CogPlatform/CageLab/manufacture/plate/europe/core_top.dxf

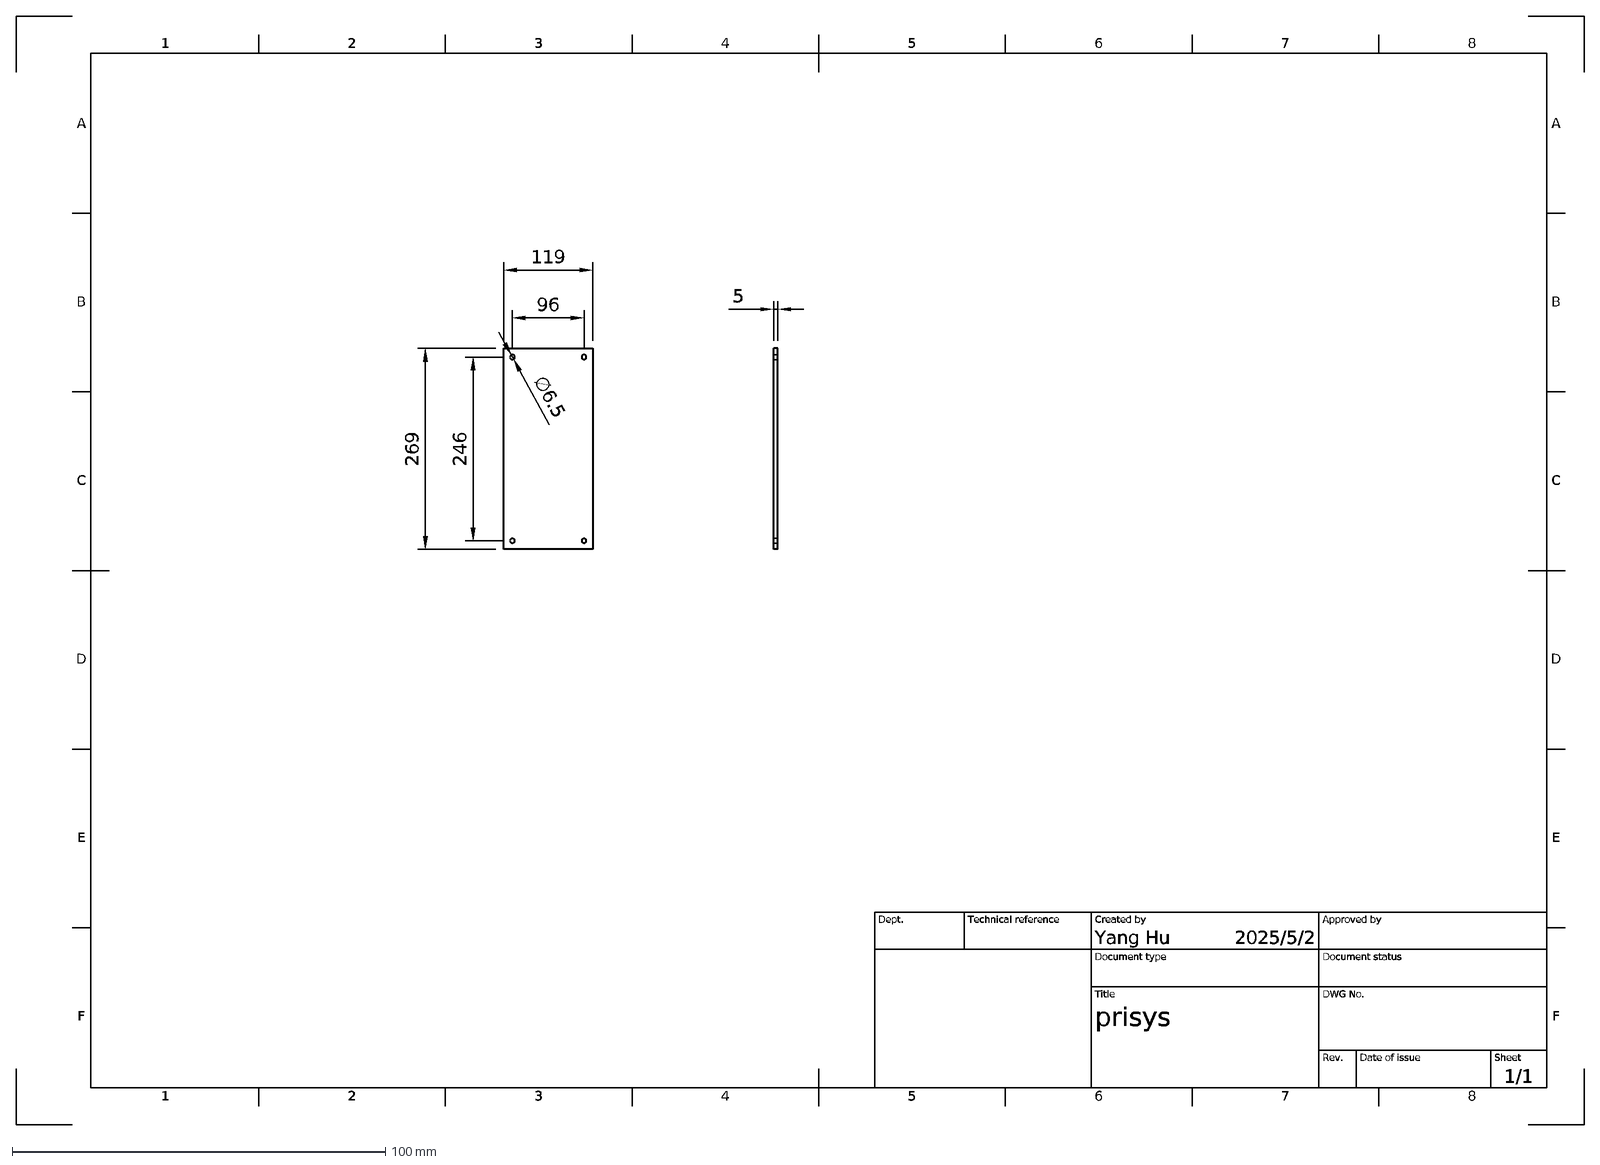
[picture p18: CAD file, 2025-05-02]
manufacture/plate/europe/core_top.dxf
1
A
2
3
4
5
6
7
8
B
C
D
E
F
2025/5/2
1/1
prisys
Yang Hu
Dept.
Technical reference
Created by
Approved by
Document type
Document status
Title
DWG No.
Rev.
Date of issue
Sheet
96
119
246
269
∅6.5
