CogPlatform/CageLab/manufacture/plate/europe/display.dxf

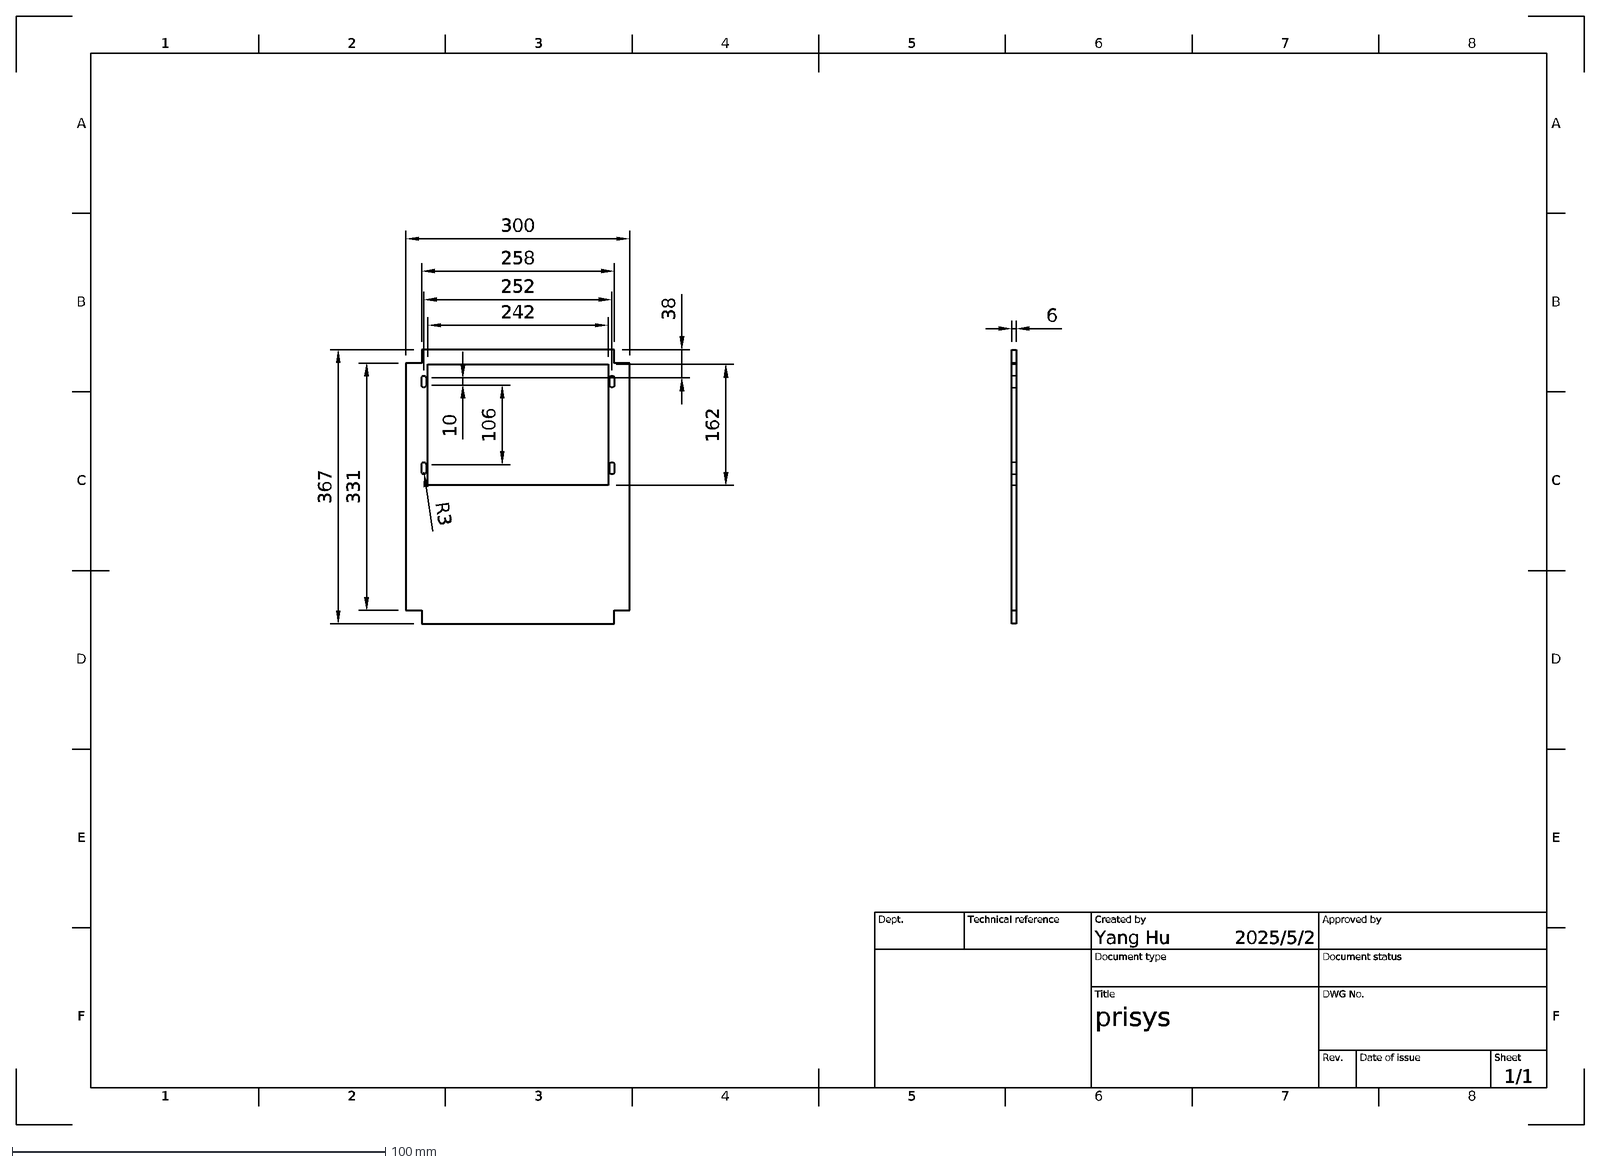
[picture p20: CAD file, 2025-05-02]
manufacture/plate/europe/display.dxf
1
A
2
3
4
5
6
7
8
B
C
D
E
F
2025/5/2
1/1
prisys
Yang Hu
Dept.
Technical reference
Created by
Approved by
Document type
Document status
Title
DWG No.
Rev.
Date of issue
Sheet
242
252
258
300
331
367
10
106
38
162
R3
