CogPlatform/CageLab/manufacture/plate/redbuilding/extra_side.dxf

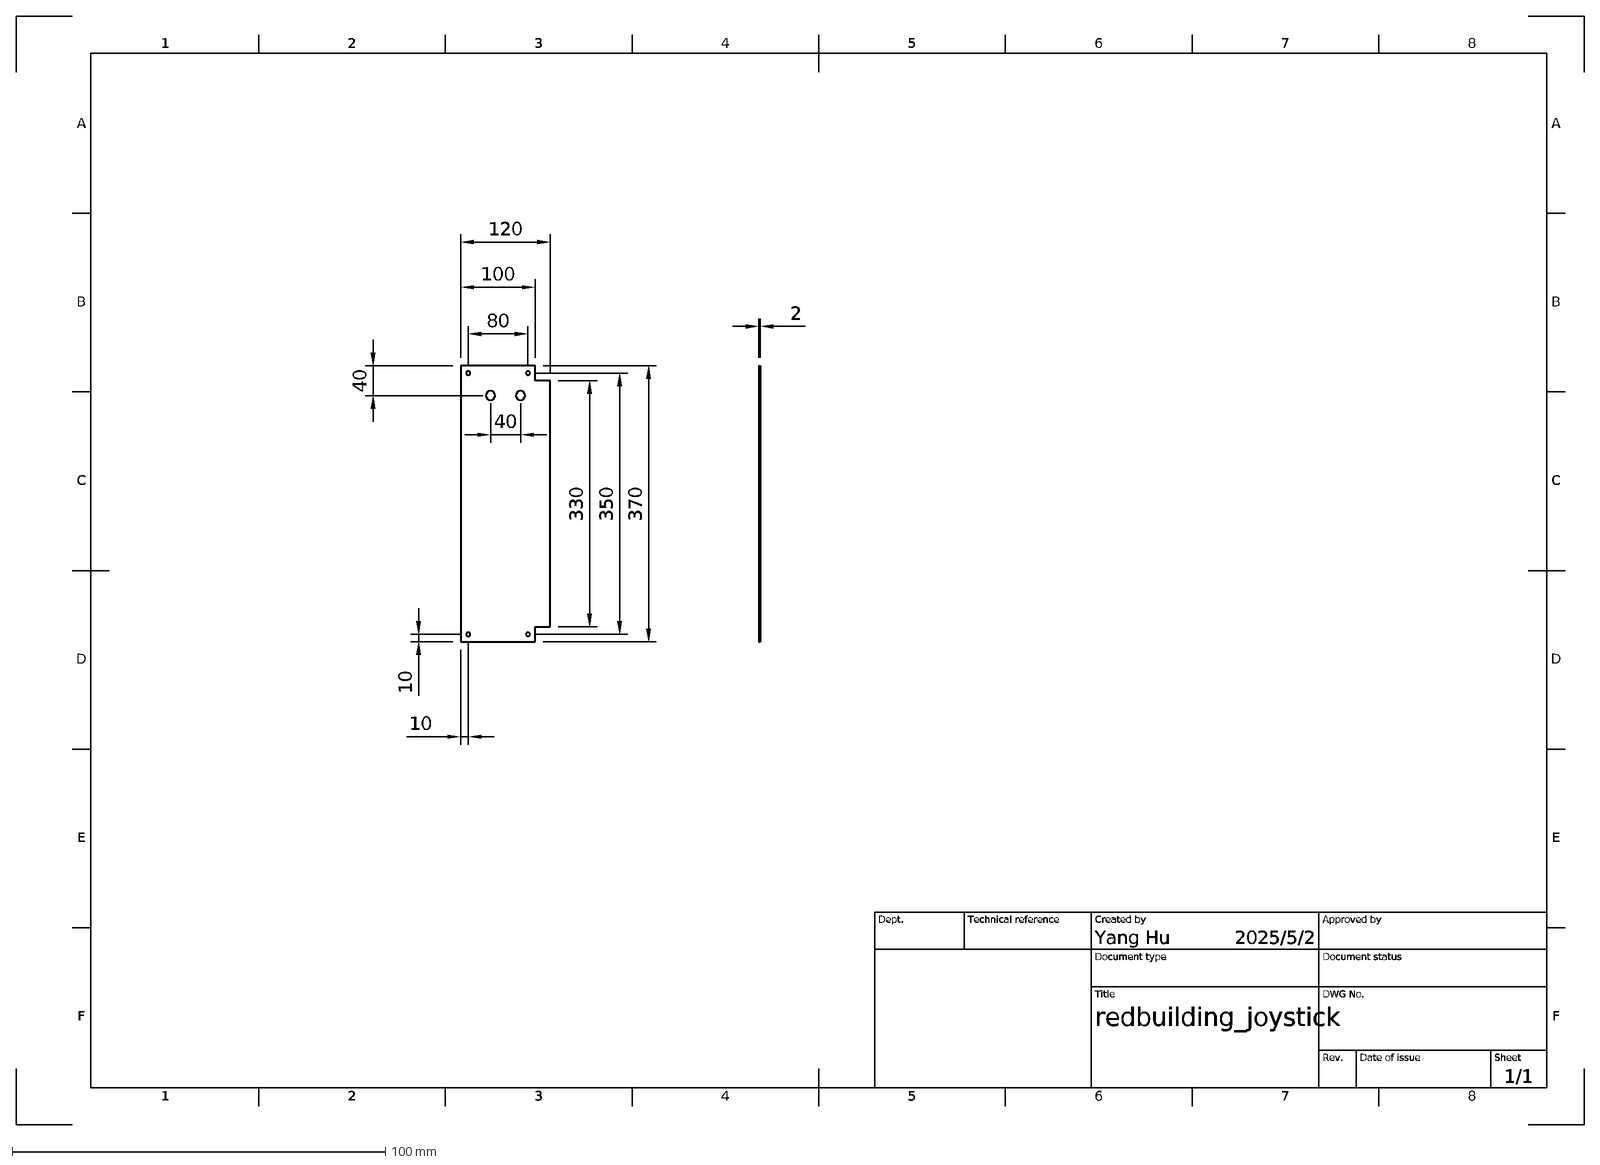
[picture p21: CAD file, 2025-05-02]
manufacture/plate/redbuilding/extra_side.dxf
1
A
2
3
4
5
6
7
8
B
C
D
E
F
2025/5/2
1/1
redbuilding_joystick
Yang Hu
Dept.
Technical reference
Created by
Approved by
Document type
Document status
Title
DWG No.
Rev.
Date of issue
Sheet
80
100
120
40
330
370
350
10
