CogPlatform/CageLab/manufacture/plate/europe/extra_top.dxf

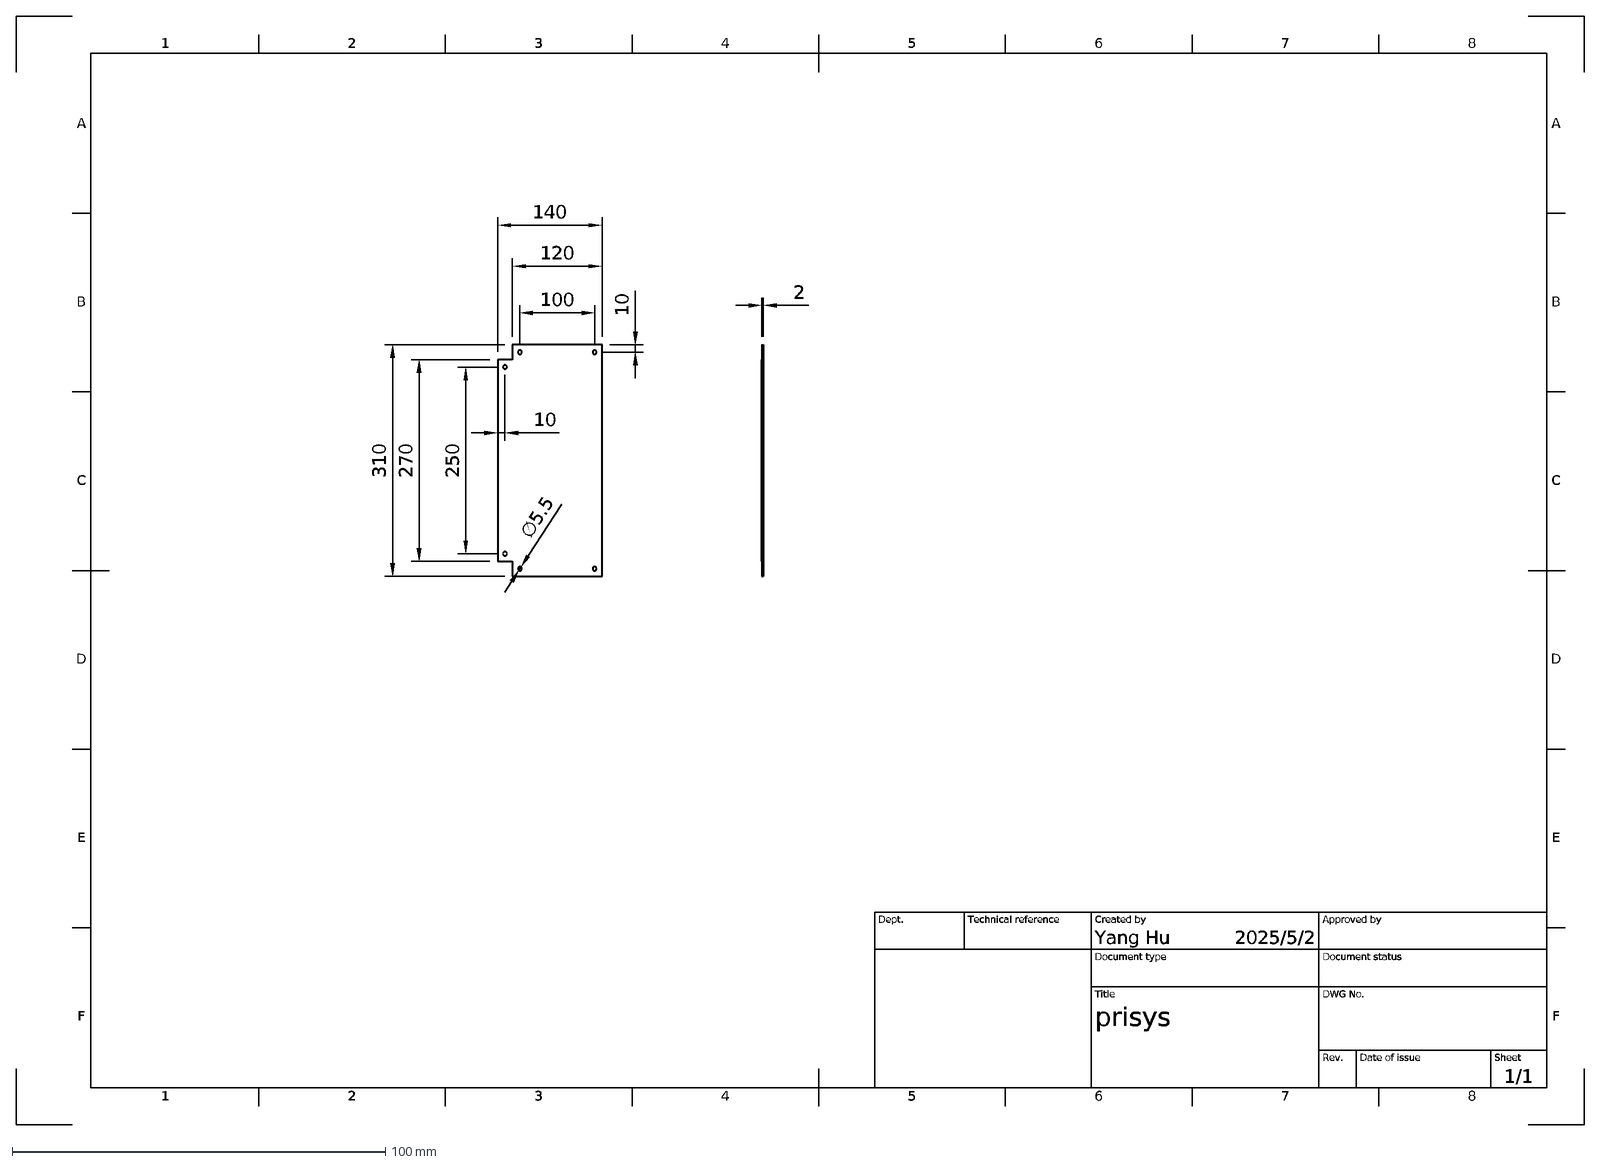
[picture p22: CAD file, 2025-05-02]
manufacture/plate/europe/extra_top.dxf
1
A
2
3
4
5
6
7
8
B
C
D
E
F
2025/5/2
1/1
prisys
Yang Hu
Dept.
Technical reference
Created by
Approved by
Document type
Document status
Title
DWG No.
Rev.
Date of issue
Sheet
100
120
140
250
270
310
10
∅5.5
