CogPlatform/CageLab/manufacture/plate/redbuilding/joystick_holder.dxf

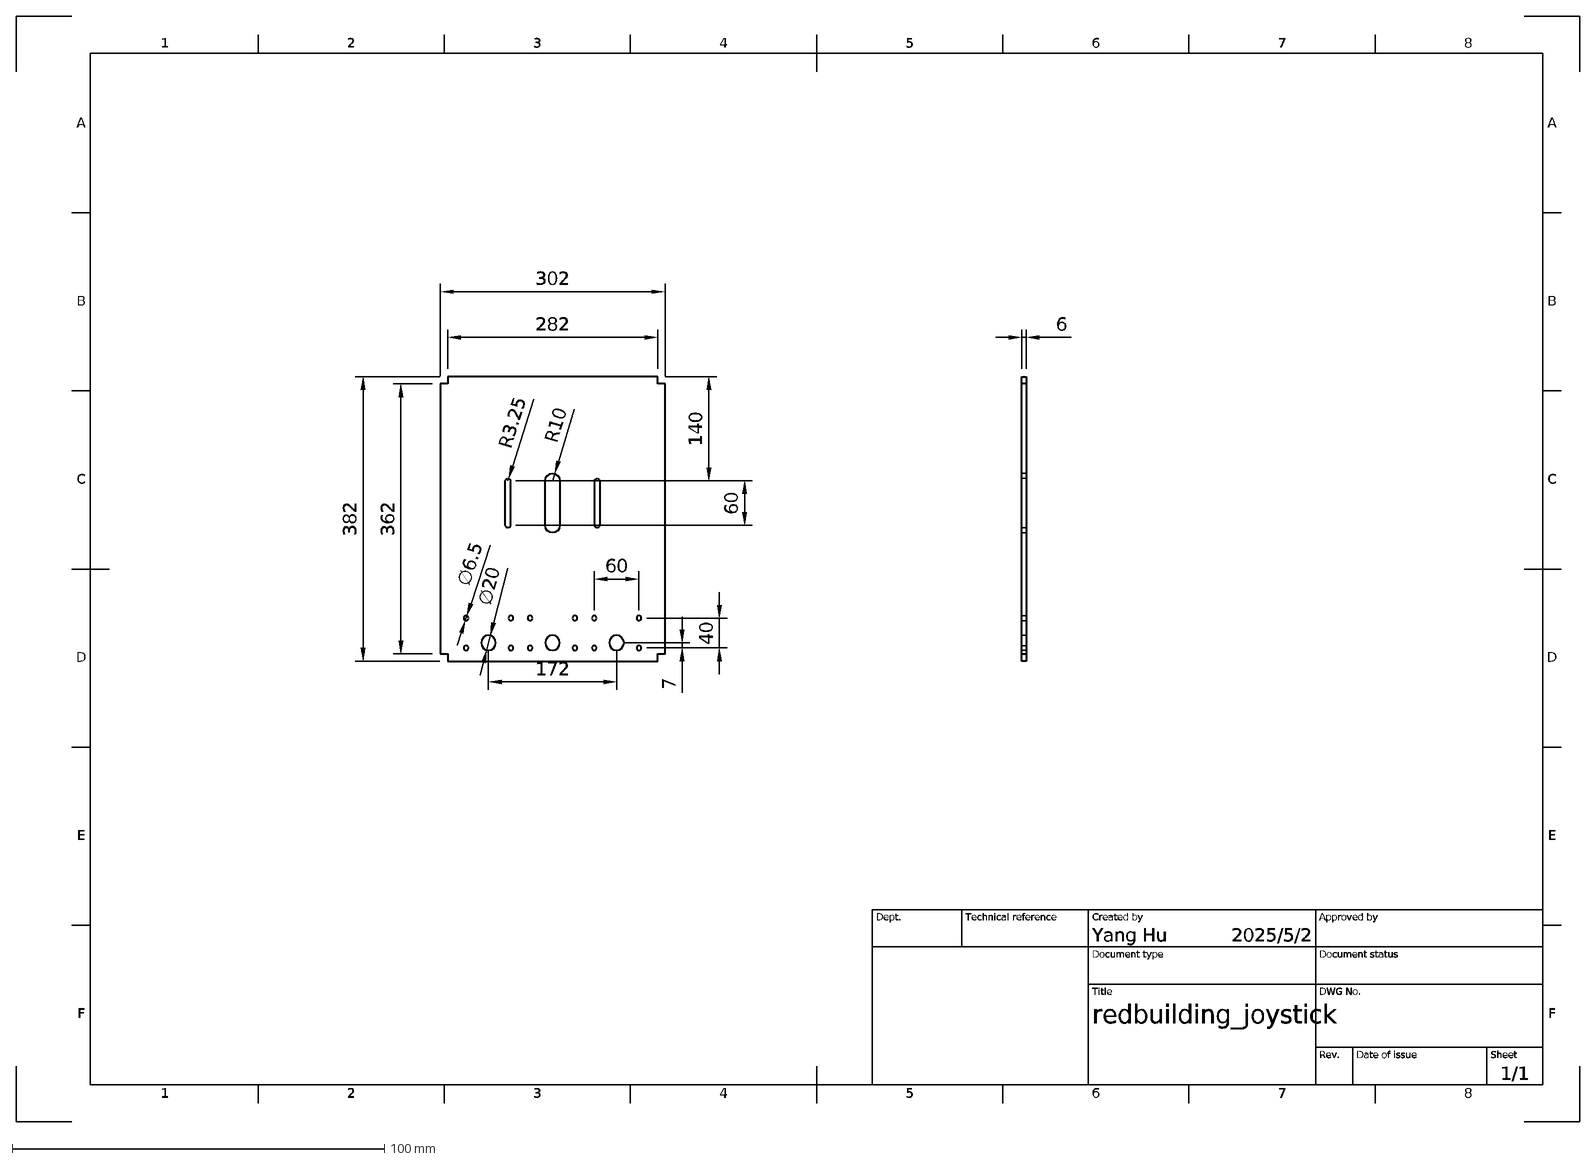
[picture p23: CAD file, 2025-05-02]
manufacture/plate/redbuilding/joystick_holder.dxf
1
A
2
3
4
5
6
7
8
B
C
D
E
F
2025/5/2
1/1
redbuilding_joystick
Yang Hu
Dept.
Technical reference
Created by
Approved by
Document type
Document status
Title
DWG No.
Rev.
Date of issue
Sheet
282
302
362
382
60
R3.25
R10
140
172
40
∅6.5
∅20
