CogPlatform/CageLab/manufacture/plate/redbuilding/redbuilding_joystick_holder.dxf

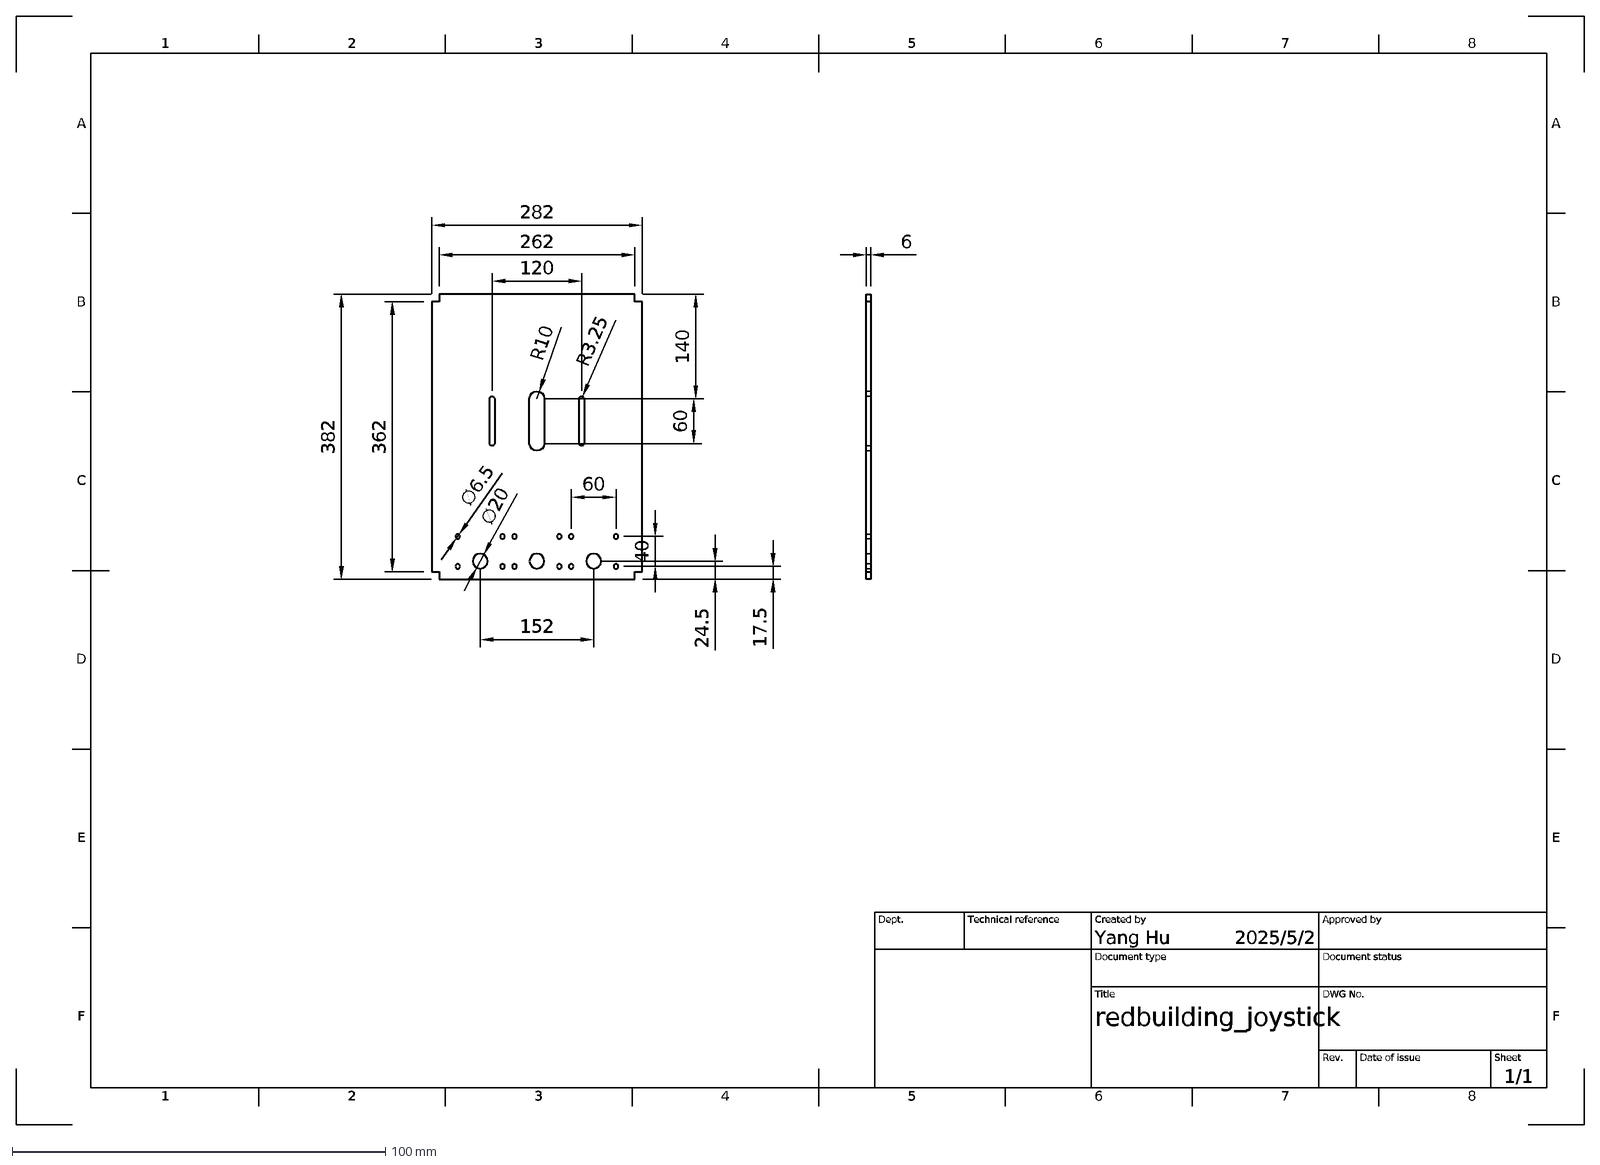
[picture p24: CAD file, 2025-05-02]
manufacture/plate/redbuilding/redbuilding_joystick_holder.dxf
1
A
2
3
4
5
6
7
8
B
C
D
E
F
2025/5/2
1/1
redbuilding_joystick
Yang Hu
Dept.
Technical reference
Created by
Approved by
Document type
Document status
Title
DWG No.
Rev.
Date of issue
Sheet
120
262
282
60
R10
R3.25
362
382
∅6.5
∅20
152
40
24.5
17.5
140
