CogPlatform/CageLab/manufacture/plate/redbuilding/display_holder.dxf

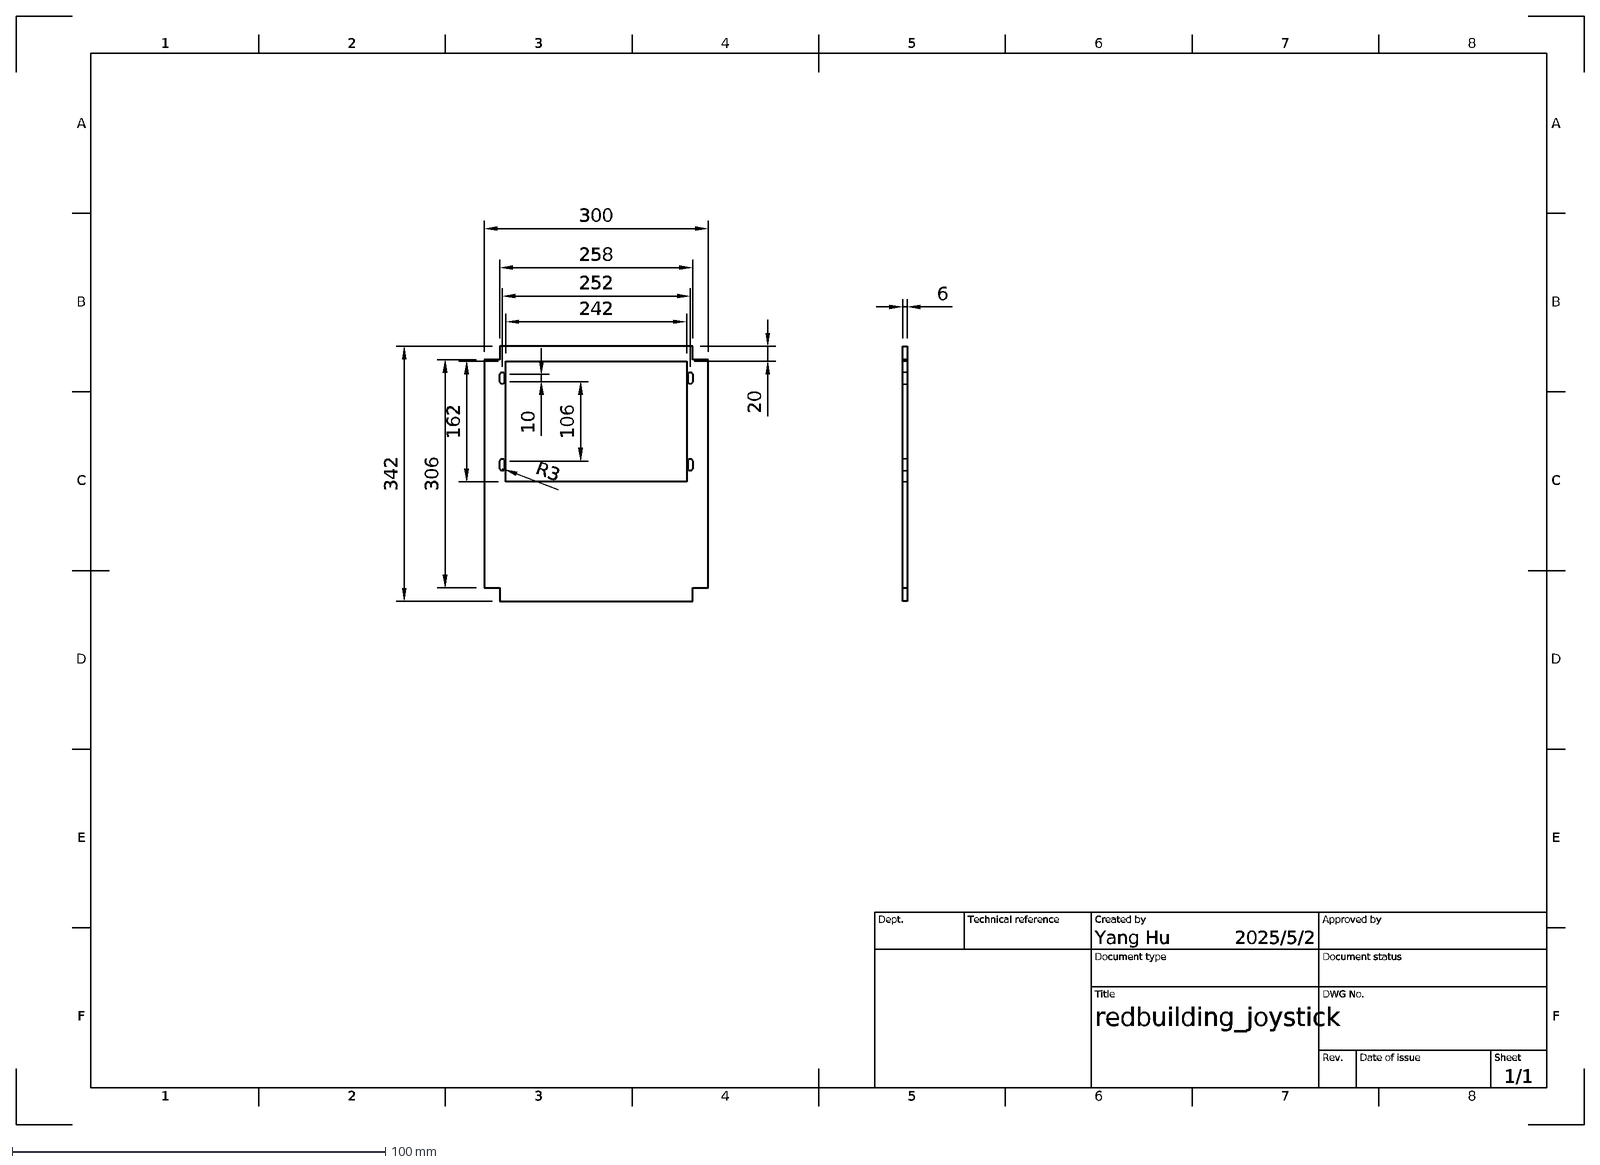
[picture p25: CAD file, 2025-05-02]
manufacture/plate/redbuilding/display_holder.dxf
1
A
2
3
4
5
6
7
8
B
C
D
E
F
2025/5/2
1/1
redbuilding_joystick
Yang Hu
Dept.
Technical reference
Created by
Approved by
Document type
Document status
Title
DWG No.
Rev.
Date of issue
Sheet
242
252
258
300
10
106
R3
162
306
342
20
